AStoker/eInk-Projects/stand-4.2in/tools/mkdrawings.py

#!/usr/bin/env python3
"""Generate dimensioned drawing sheets from the OpenSCAD model's own parameters.

Reads /tmp/params.txt (produced by `openscad -D 'part="params"'`) so the drawings
can never drift from the STLs.  Emits one SVG fragment per sheet.
"""
import math, os, json, re

P = {}
for line in open(os.environ.get("PARAMS", "/tmp/params.txt")):
    line = line.strip()
    if not line or "=" not in line:
        continue
    k, v = line.split("=", 1)
    try:
        P[k] = float(v)
    except ValueError:
        P[k] = v

# ----------------------------------------------------------------- svg utils
AR = 1.6           # arrowhead length
TS = 3.0           # default text size
out = []


def esc(s):
    return (str(s).replace("&", "&amp;").replace("<", "&lt;").replace(">", "&gt;")
            .replace("\u00b7", "&#183;").replace("\u2264", "&#8804;")
            .replace("\u00b0", "&#176;").replace("\u00d7", "&#215;"))


def n(v):
    """format a number the way a drawing would"""
    if abs(v - round(v)) < 0.005:
        return f"{v:.0f}"
    return f"{v:.2f}".rstrip("0").rstrip(".")


class SVG:
    def __init__(self, w, h):
        self.w, self.h, self.b = w, h, []

    def add(self, s):
        self.b.append(s)

    def line(self, x1, y1, x2, y2, cls="edge"):
        self.add(f'<line class="{cls}" x1="{x1:.2f}" y1="{y1:.2f}" x2="{x2:.2f}" y2="{y2:.2f}"/>')

    def rect(self, x, y, w, h, cls="edge", r=0):
        self.add(f'<rect class="{cls}" x="{x:.2f}" y="{y:.2f}" width="{w:.2f}" '
                 f'height="{h:.2f}" rx="{r:.2f}"/>')

    def circ(self, x, y, d, cls="edge"):
        self.add(f'<circle class="{cls}" cx="{x:.2f}" cy="{y:.2f}" r="{d/2:.2f}"/>')

    def path(self, d, cls="edge"):
        self.add(f'<path class="{cls}" d="{d}"/>')

    def txt(self, x, y, s, cls="lbl", anchor="middle", size=TS, rot=None):
        tr = f' transform="rotate({rot} {x:.2f} {y:.2f})"' if rot else ""
        self.add(f'<text class="{cls}" x="{x:.2f}" y="{y:.2f}" text-anchor="{anchor}" '
                 f'font-size="{size}"{tr}>{esc(s)}</text>')

    # --- dimensioning -----------------------------------------------------
    def _ah(self, x, y, dx, dy):
        """arrowhead at (x,y) pointing along (dx,dy)"""
        m = math.hypot(dx, dy) or 1
        dx, dy = dx / m, dy / m
        px, py = -dy, dx
        return (f'M{x:.2f},{y:.2f} L{x-dx*AR+px*AR*0.32:.2f},{y-dy*AR+py*AR*0.32:.2f} '
                f'L{x-dx*AR-px*AR*0.32:.2f},{y-dy*AR-py*AR*0.32:.2f} Z')

    def dimh(self, x1, x2, y, label=None, ext_from=None, flip=False):
        if label is None:
            label = n(abs(x2 - x1))
        if ext_from is not None:
            for x in (x1, x2):
                self.line(x, ext_from, x, y + (1.2 if y > ext_from else -1.2), "ext")
        self.line(x1, y, x2, y, "dim")
        inside = abs(x2 - x1) > 9
        if inside:
            self.path(self._ah(x1, y, x1 - x2, 0), "arrow")
            self.path(self._ah(x2, y, x2 - x1, 0), "arrow")
        else:
            self.line(x1 - 4, y, x1, y, "dim")
            self.line(x2, y, x2 + 4, y, "dim")
            self.path(self._ah(x1, y, 1, 0), "arrow")
            self.path(self._ah(x2, y, -1, 0), "arrow")
        tx = (x1 + x2) / 2
        if inside:
            self.txt(tx, y - 1.3, label, "dimtxt")
        else:
            self.txt(tx, y - 1.6 if not flip else y + 3.4, label, "dimtxt")

    def dimv(self, y1, y2, x, label=None, ext_from=None):
        if label is None:
            label = n(abs(y2 - y1))
        if ext_from is not None:
            for y in (y1, y2):
                self.line(ext_from, y, x + (1.2 if x > ext_from else -1.2), y, "ext")
        self.line(x, y1, x, y2, "dim")
        inside = abs(y2 - y1) > 9
        if inside:
            self.path(self._ah(x, y1, 0, y1 - y2), "arrow")
            self.path(self._ah(x, y2, 0, y2 - y1), "arrow")
        else:
            self.line(x, y1 - 4, x, y1, "dim")
            self.line(x, y2, x, y2 + 4, "dim")
            self.path(self._ah(x, y1, 0, 1), "arrow")
            self.path(self._ah(x, y2, 0, -1), "arrow")
        self.txt(x - 1.3, (y1 + y2) / 2, label, "dimtxt", rot=-90)

    def leader(self, x, y, tx, ty, label, anchor="start"):
        self.line(x, y, tx, ty, "dim")
        self.path(self._ah(x, y, x - tx, y - ty), "arrow")
        off = 1.2 if anchor == "start" else -1.2
        self.txt(tx + off, ty + 1.0, label, "note", anchor)

    def note(self, x, y, label, anchor="start", size=2.7):
        self.txt(x, y, label, "note", anchor, size)

    def hatch(self, x, y, w, h, step=1.6):
        self.add(f'<g class="hatch" clip-path="url(#c{abs(hash((x,y,w,h)))%99999})">')
        self.add(f'<clipPath id="c{abs(hash((x,y,w,h)))%99999}">'
                 f'<rect x="{x:.2f}" y="{y:.2f}" width="{w:.2f}" height="{h:.2f}"/></clipPath>')
        k = -h
        while k < w:
            self.line(x + k, y + h, x + k + h, y, "hl")
            k += step
        self.add('</g>')

    def titleblock(self, x, y, w, h, name, sheet, of, scale, rev="E"):
        # the sheets are always drawn in the as-designed hand; this says whether
        # the exported STLs come out that way or mirrored
        self.txt(x, y - 2.4,
                 "STLs export flat-face-down and MIRRORED IN X (print_mirror = true)"
                 if MIRRORED else
                 "STLs export flat-face-down, as drawn (print_mirror = false)",
                 "note", "start", 2.35)
        self.rect(x, y, w, h, "tbframe")
        self.line(x, y + h * 0.5, x + w, y + h * 0.5, "tbrule")
        self.line(x + w * 0.55, y + h * 0.5, x + w * 0.55, y + h, "tbrule")
        self.line(x + w * 0.78, y + h * 0.5, x + w * 0.78, y + h, "tbrule")
        self.txt(x + 2, y + h * 0.34, name, "tbname", "start", 3.6)
        self.txt(x + 2, y + h * 0.85, f"UNITS mm · SCALE {scale}", "tbmeta", "start", 2.4)
        self.txt(x + w * 0.575, y + h * 0.85, f"SHEET {sheet}/{of}", "tbmeta", "start", 2.4)
        self.txt(x + w * 0.80, y + h * 0.85, f"REV {rev}", "tbmeta", "start", 2.4)


    def bal(self, x, y, num, tx, ty):
        self.line(x, y, tx, ty, "dim")
        self.path(self._ah(x, y, x - tx, y - ty), "arrow")
        self.circ(tx, ty, 5.6, "balloon")
        self.txt(tx, ty + 1.15, str(num), "baltxt", size=3.1)

    def notes(self, x, y, items, cw=46, title="NOTES"):
        import textwrap
        if title:
            self.txt(x, y, title, "vlabel", "start", 3.2)
            y += 6.5
        for num, text in items:
            self.circ(x + 2.8, y - 1.0, 5.6, "balloon")
            self.txt(x + 2.8, y + 0.15, str(num), "baltxt", size=3.1)
            lines = textwrap.wrap(text, cw) or [""]
            for j, ln in enumerate(lines):
                self.txt(x + 9, y + j * 3.7, ln, "note", "start", 2.7)
            y += max(1, len(lines)) * 3.7 + 2.8
        return y

    def render(self, ident):
        return (f'<svg class="dwg" id="{ident}" viewBox="0 0 {self.w} {self.h}" '
                f'xmlns="http://www.w3.org/2000/svg" role="img">'
                + "".join(self.b) + "</svg>")


# ------------------------------------------------------- standalone sheet CSS
# The sheets are written twice: as fragments in _sheets.json (styled by the page
# in tools/mkpage.py) and as standalone .svg files.  A standalone file has no
# page around it, so it carries its own copy of the drawing classes - that is
# what lets the README embed a sheet directly, and what makes a sheet readable
# when the file is opened on its own.
#
# The colours are written out literally, once per theme, rather than as CSS
# custom properties: an SVG loaded through <img> (which is how a README embeds
# one) is rendered by whatever engine the viewer has, and var() is the first
# thing a lightweight renderer drops - it takes the whole drawing to black.
LIGHT = dict(paper="#F1F3F0", surface="#FAFBF9", ink="#171B18", ink2="#59635C",
             rule="#D3D8D2", accent="#0E6B57", verify="#A8631A", partf="#E4E8E3",
             glass="#D9E4E6", pcbf="#CBDCCF", cellf="#D2D6D8", chgf="#C7D8E4",
             platf="#EDEFEA", bossf="#DCE2DA", padf="#D8DED6", voidf="#E7EAE5")
DARK  = dict(paper="#0F1211", surface="#171B18", ink="#E8ECE7", ink2="#93A099",
             rule="#2C332E", accent="#57CFA9", verify="#E0A64B", partf="#232A26",
             glass="#243233", pcbf="#1F3327", cellf="#2A3033", chgf="#1E2E3A",
             platf="#1C221E", bossf="#28302B", padf="#2A322C", voidf="#101413")

RULES = """
svg{{font-family:"IBM Plex Mono",ui-monospace,monospace}}
.bg{{fill:{paper};stroke:none}}
.part{{fill:{partf};stroke:{ink};stroke-width:.55}}
.edge{{fill:none;stroke:{ink};stroke-width:.5}}
.inkline{{fill:none;stroke:{ink};stroke-width:1.1}}
.ghost{{fill:none;stroke:{rule};stroke-width:.45}}
.hid{{fill:none;stroke:{ink2};stroke-width:.35;stroke-dasharray:2.2 1.4}}
.cl{{fill:none;stroke:{ink2};stroke-width:.28;stroke-dasharray:6 1.6 1 1.6;opacity:.75}}
.cut{{fill:{paper};stroke:{ink};stroke-width:.45}}
.ink{{fill:{ink};opacity:.86;stroke:none}}
.glass{{fill:{glass};stroke:{ink};stroke-width:.4}}
.pcb{{fill:{pcbf};stroke:{ink};stroke-width:.45}}
.cell{{fill:{cellf};stroke:{ink};stroke-width:.45}}
.chg{{fill:{chgf};stroke:{ink};stroke-width:.4}}
.plat{{fill:{platf};stroke:{ink2};stroke-width:.35}}
.boss{{fill:{bossf};stroke:{ink2};stroke-width:.35}}
.pad{{fill:{padf};stroke:{ink2};stroke-width:.35}}
.voidfill{{fill:{voidf};stroke:{ink2};stroke-width:.35}}
.warn{{fill:none;stroke:{verify};stroke-width:.6;stroke-dasharray:2 1.2}}
.wire{{fill:none;stroke:{ink};stroke-width:.62;stroke-linejoin:round}}
.wire.ntc{{stroke:{verify}}}
.clash{{fill:{verify};fill-opacity:.30;stroke:{verify};stroke-width:.7}}
.clashtxt{{fill:{verify};font-weight:600;letter-spacing:.02em}}
.res{{fill:{surface};stroke:{ink};stroke-width:.5}}
.leg{{stroke:{ink};stroke-width:2.6;stroke-linecap:round;fill:none}}
.table{{stroke:{ink2};stroke-width:.6}}
.com{{fill:{verify};stroke:{ink};stroke-width:.3}}
.hl{{stroke:{rule};stroke-width:.3;fill:none}}
.hatch{{opacity:.9}}
.dim{{fill:none;stroke:{accent};stroke-width:.32}}
.ext{{fill:none;stroke:{accent};stroke-width:.22;opacity:.55}}
.arrow{{fill:{accent};stroke:none}}
.dimtxt{{fill:{accent};letter-spacing:.02em}}
.note{{fill:{ink2}}}
.val{{fill:{ink};font-weight:600}}
.val.warn{{fill:{verify};stroke:none}}
.balloon{{fill:{surface};stroke:{accent};stroke-width:.45}}
.baltxt{{fill:{accent};font-weight:600;text-anchor:middle}}
.vlabel{{fill:{ink};font-weight:600;letter-spacing:.09em}}
.cmp{{fill:{ink};font-weight:600}}
.cmpsub{{fill:{ink2}}}
.tbframe{{fill:none;stroke:{ink};stroke-width:.5}}
.tbrule{{stroke:{rule};stroke-width:.35;fill:none}}
.tbname{{fill:{ink};font-weight:700;letter-spacing:.03em}}
.tbmeta{{fill:{ink2};letter-spacing:.09em}}
"""

SVG_CSS = (RULES.format(**LIGHT)
           + "@media (prefers-color-scheme:dark){" + RULES.format(**DARK) + "}")


def standalone(sv):
    """Wrap a sheet fragment as a file that renders on its own.

    Size and background come from the fragment's own viewBox - sheet 8 is a
    taller sheet than the rest, and a hard-coded background left it striped.
    """
    w, h = (float(v) for v in re.search(r'viewBox="0 0 ([\d.]+) ([\d.]+)"', sv).groups())
    return ('<?xml version="1.0" encoding="UTF-8"?>\n'
            + sv.replace('class="dwg"', f'class="dwg" width="{w*4:.0f}" height="{h*4:.0f}"')
                .replace('role="img">',
                         f'role="img"><style>{SVG_CSS}</style>'
                         f'<rect class="bg" x="0" y="0" width="{w:.0f}" height="{h:.0f}"/>', 1))


# ------------------------------------------------------------------ geometry
W, H, D = P["W"], P["H"], P["depth"]
FLASH = bool(P.get("flash_port", 0))          # is the driver board's USB-C cut through?
MIRRORED = bool(P.get("print_mirror", 0))     # do the STLs come out the opposite hand?
HEADER = bool(P.get("mod_header", 0))         # is a mated module header being allowed for?
BARE   = bool(P.get("bare_panel", 0))         # panel with no PCB behind it?
INSERT = bool(P.get("insert_fit", 0))         # heat-set inserts, or self-tapping?
PERF   = bool(P.get("perf_fit", 0))           # is a separate divider board fitted?
CARRIER= bool(P.get("carrier_fit", 0))        # driver on a carrier perfboard?
MAGS   = bool(P.get("mag_fit", 0))            # fridge magnets in the back face?
SNAP   = bool(P.get("port_snap", 0))          # rear port is a snap-in pigtail?
CLAMP  = bool(P.get("pivot_screw", 0))        # hinge is a clamp screw, not a pin?
FAST   = (f"M3 heat-set inserts (bore dia {P['ins_d']:g} x {P['ins_l']+1:g} deep) with countersunk screws"
          if INSERT else "self-tapping screws")
# screw positions, [x, z].  Bare panel: one near each corner, through the end
# walls.  Module: the old single spine of three, all on the +X side.
SCR = ([(-P["scr_cx"], P["scr_cz"]), (P["scr_cx"], P["scr_cz"]),
        (-P["scr_cx"], P["H"]-P["scr_cz"]), (P["scr_cx"], P["H"]-P["scr_cz"])] if BARE
       else [(P["scr_x"], P["scr_z0"]), (P["scr_x"], P["scr_z1"]), (P["scr_x"], P["scr_z2"])])
P["flash_skin"] = P["flash_wall"]             # material left outboard of a closed jack
cav_x0, cav_x1 = P["cav_x0"], P["cav_x1"]
cav_z0, cav_z1 = P["cav_z0"], P["cav_z1"]
cav_w, cav_h = P["cav_w"], P["cav_h"]
Zc = P["Zc"]
# ---- the stand, PORTRAIT ONLY.  The leg pivots directly in a recess in the
# cover, so every stand view on these sheets is a rectangle and an arc.
piv_z, piv_y, piv_h = P["piv_z"], P["piv_y"], P["piv_h"]
rec_w, rec_top, rec_y0 = P["rec_w"], P["rec_top"], P["rec_y0"]
rec_z0 = P["rec_z0"]                           # recess, bottom end (derived in the model)
DEP    = P["dep_ang"]
win_w, win_h = P["win_w"], P["win_h"]
SW, SH = 268, 190
TBX, TBY = SW - 96 - 6, SH - 18 - 5

def mk(w=SW, h=SH):
    return SVG(w, h)

# The port opening, as the model actually cuts it.  With port_snap the pigtail's
# own catch holds it: the opening is snap_w x snap_h plus clearance and there is
# nothing printed around it.  Without it, a breakout board sits in printed rails
# behind a smaller port_w x port_h receptacle hole.  Drawing the rails
# unconditionally showed features this build does not have.
def port_opening(s, mx, mz, cls="cut"):
    if SNAP:
        w = P["snap_w"] + 2*P["snap_c"]
        h = P["snap_h"] + 2*P["snap_c"]
        s.rect(mx(P["ucb_x"] - w/2), mz(P["ucb_z"] + h/2), w, h, cls, 0.6)
        return w, h
    for sz in (-1, 1):
        s.rect(mx(P["ucb_x"] - (P["ucb_w"]+4)/2),
               mz(P["ucb_z"] + sz*(P["ucb_t"]/2+0.15+1.0) + 1.0),
               P["ucb_w"]+4, 2.0, "boss")
    s.rect(mx(P["ucb_x"] - P["port_w"]/2), mz(P["ucb_z"] + P["port_h"]/2),
           P["port_w"], P["port_h"], cls, 1.2)
    return P["port_w"], P["port_h"]


def views(s, ox, oy):
    return (lambda x: ox + x + W/2), (lambda z: oy + (H - z))

# ============================================================ SHEET 1
def sheet1():
    s = mk()
    oy = 15
    fx, fz = views(s, 24, oy)

    s.rect(fx(-W/2), fz(H), W, H, "part", P["corner_r"])
    s.rect(fx(-win_w/2), fz(Zc + win_h/2), win_w, win_h, "edge", 3)
    s.rect(fx(-P["act_w"]/2), fz(Zc + P["act_h"]/2), P["act_w"], P["act_h"], "ink")
    s.rect(fx(P["pcb_px"]-P["pcb_w"]/2), fz(Zc+P["pcb_h"]/2), P["pcb_w"], P["pcb_h"], "hid")
    s.line(fx(0), fz(H)-4, fx(0), fz(0)+4, "cl")
    s.line(fx(-W/2)-4, fz(Zc), fx(W/2)+4, fz(Zc), "cl")
    s.txt(fx(0), fz(H)-8, "FRONT", "vlabel")
    s.dimh(fx(-W/2), fx(W/2), fz(0)+16, n(W), ext_from=fz(0))
    s.dimv(fz(H), fz(0), fx(-W/2)-13, n(H), ext_from=fx(-W/2))
    s.dimh(fx(-win_w/2), fx(win_w/2), fz(0)+8, n(win_w), ext_from=fz(Zc-win_h/2))
    s.dimv(fz(Zc+win_h/2), fz(Zc-win_h/2), fx(-W/2)-5, n(win_h), ext_from=fx(-win_w/2))
    s.dimh(fx(-W/2), fx(-win_w/2), fz(H)-5, n(W/2-win_w/2), ext_from=fz(Zc+win_h/2))
    s.dimh(fx(win_w/2), fx(W/2), fz(H)-5, n(W/2-win_w/2), ext_from=fz(Zc+win_h/2))
    s.dimv(fz(H), fz(Zc+win_h/2), fx(W/2)+6, n(H/2-win_h/2), ext_from=fx(win_w/2))
    s.dimv(fz(Zc-win_h/2), fz(0), fx(W/2)+6, n(H/2-win_h/2), ext_from=fx(win_w/2))
    s.bal(fx(-win_w/2+0.7), fz(Zc+win_h/2-4), 1, fx(-win_w/2-6), fz(Zc+win_h/2+7))
    s.bal(fx(-W/2+2.4), fz(2.4), 2, fx(-W/2+11), fz(11))

    # side
    sx = 124
    yx = lambda y: sx + y
    s.rect(yx(0), fz(H), D, H, "part")
    s.line(yx(P["body_d"]), fz(H), yx(P["body_d"]), fz(0), "hid")
    ch, rc = P["front_chf"], P["rear_chf"]
    s.line(yx(0), fz(H)+ch, yx(ch), fz(H), "edge")
    s.line(yx(0), fz(0)-ch, yx(ch), fz(0), "edge")
    s.line(yx(D-rc), fz(H), yx(D), fz(H)+rc, "edge")
    s.line(yx(D-rc), fz(0), yx(D), fz(0)-rc, "edge")
    # the flash opening only exists if the model cuts it; otherwise the wall is
    # solid and all that is behind it is a blind pocket, drawn hidden
    s.rect(yx(P["flash_y0"]), fz(H), P["flash_y1"]-P["flash_y0"], 1.6,
           "cut" if FLASH else "hid")
    s.rect(yx(D-1.0), fz(P["ucb_z"]+P["port_h"]/2), 1.0, P["port_h"], "cut")
    s.txt(yx(D/2), fz(H)-8, "RIGHT", "vlabel")
    s.dimh(yx(0), yx(D), fz(0)+16, n(D), ext_from=fz(0))
    s.bal(yx(D-rc/2), fz(H)+rc/2, 3, yx(D)+9, fz(H)-6)
    s.bal(yx(ch/2), fz(0)-ch/2, 4, yx(D)+9, fz(0)+8)
    s.bal(yx((P["flash_y0"]+P["flash_y1"])/2), fz(H)+0.8, 5, yx(D)+9, fz(H)+9)
    s.bal(yx(D), fz(P["ucb_z"]), 6, yx(D)+9, fz(P["ucb_z"])+2)
    s.bal(yx(P["body_d"]), fz(30), 7, yx(D)+9, fz(30))

    # back
    bx = 156
    gx = lambda x: bx + x + W/2
    s.rect(gx(-W/2), fz(H), W, H, "part", P["corner_r"])
    s.rect(gx(-rec_w/2), fz(rec_top), rec_w, rec_top-rec_z0, "edge", 1)
    s.rect(gx(-P["leg_w"]/2), fz(piv_z+P["heel_z"]), P["leg_w"],
           piv_z+P["heel_z"]-P["foot_z"], "hid", 1)
    pw, ph = port_opening(s, gx, fz)
    for (sx, sz) in SCR:
        s.circ(gx(sx), fz(sz), P["scr_head"], "cut")
    s.line(gx(0), fz(H)-4, gx(0), fz(0)+4, "cl")
    s.line(gx(-W/2)-4, fz(piv_z), gx(W/2)+4, fz(piv_z), "cl")
    s.txt(gx(0), fz(H)-8, "BACK", "vlabel")
    s.dimv(fz(piv_z), fz(0), gx(-W/2)-8, n(piv_z), ext_from=gx(-W/2))
    s.dimh(gx(0), gx(P["ucb_x"]), fz(0)+8, n(abs(P["ucb_x"])), ext_from=fz(P["ucb_z"]))
    s.dimv(fz(P["ucb_z"]), fz(0), gx(P["ucb_x"])-8, n(P["ucb_z"]), ext_from=gx(P["ucb_x"]))
    s.dimh(gx(SCR[-1][0]), gx(W/2), fz(H)-5, n(W/2-SCR[-1][0]), ext_from=fz(SCR[-1][1]))
    s.bal(gx(P["ucb_x"]+pw/2), fz(P["ucb_z"]), 6, gx(P["ucb_x"]+18), fz(P["ucb_z"])+9)
    s.bal(gx(SCR[0][0]), fz(SCR[0][1]), 8, gx(SCR[0][0])-11, fz(SCR[0][1])+8)
    s.bal(gx(rec_w/2), fz(piv_z+8), 9, gx(rec_w/2)+10, fz(piv_z+8)-7)

    y = s.notes(22, 143, [
        (1, f"panel white border {n(P['white_show_short'])} visible on the short axis, "
            f"{n(P['white_show_long'])} on the long axis"),
        (2, f"outer corners R{n(P['corner_r'])}"),
        (3, f"{n(rc)} x 45 deg chamfer on all four back edges. It moves the contact edge forward - see sheet 7"),
        (4, f"{n(ch)} x 45 deg chamfer on the front face"),
    ], cw=44)
    s.notes(108, 143, [
        (5, f"USB-C flash port, {n(P['usb_w'])} wide, top wall (driver board)"
            if FLASH else
            f"driver-board USB-C, {n(P['usb_w'])} wide - blind pocket, the top wall "
            f"is solid ({n(P['wall'])} thick, {n(P['flash_skin'])} of skin left). "
            f"The charge port is the only opening"),
        (6, f"USB-C charge port {n(P['port_w'])} x {n(P['port_h'])}, back face"),
        (7, "frame / cover seam"),
    ], cw=44, title=" ")
    s.notes(190, 143, [
        (8, f"4 x cover screws, one near each corner: {n(P['scr_cx'])} from the centreline, {n(P['scr_cz'])} from each end. {FAST}"
            if BARE else
            f"3 x M2.5 cover screws, {n(P['scr_x'])} from the centreline"),
        (9, f"kickstand leg {n(P['leg_w'])} wide, folded FLUSH in a {n(rec_w)} recess; "
            f"pivot {n(piv_z)} up. The folded foot stops at z {n(P['foot_z'])}, clear of the "
            f"{n(rc)} chamfer, so nothing overhangs the bottom edge"),
    ], cw=40, title=" ")
    s.titleblock(TBX, TBY, 96, 18, "ASSEMBLY / ENVELOPE", 1, 8, "1:1")
    return s.render("s1")


# ============================================================ SHEET 2
def sheet2():
    s = mk()
    ox, oy = 28, 14
    fx, fz = views(s, ox, oy)
    s.rect(fx(-W/2), fz(H), W, H, "ghost", P["corner_r"])
    s.rect(fx(cav_x0), fz(cav_z1), cav_w, cav_h, "part", P["cav_r"])
    s.rect(fx(-rec_w/2), fz(rec_top), rec_w, rec_top-rec_z0, "hid", 1)
    # fridge magnet pockets - blind in the BACK face, so hidden from in here
    if MAGS:
        for mx, mz in ((P["mag_x"], P["mag_z0"]), (-P["mag_x"], P["mag_z1"])):
            s.circ(fx(mx), fz(mz), P["mag_bd"], "boss")   # the boss, on this face
            s.circ(fx(mx), fz(mz), P["mag_bore"], "hid")  # the pocket, behind it
    # the register extension: the plate that floors the shallow end of the pocket.
    # It stops short of the bottom edge on purpose - see note 1.
    s.rect(fx(-P["stand_reg_w"]/2), fz(P["shl_z0"]+0.05),
           P["stand_reg_w"], (P["shl_z0"]+0.05)-P["reg_ext_z0"], "boss")

    # ---- the cell, bottom band, centred
    bx0, bz0 = P["bat_x0"], P["bat_cz"]-P["bat_h"]/2
    s.rect(fx(bx0), fz(bz0+P["bat_h"]), P["bat_w"], P["bat_h"], "cell", 2)
    s.txt(fx(P["bat_cx"]), fz(P["bat_cz"])-1.4, "LiPo 2000 mAh  ·  694449", "cmp", size=3.0)
    s.txt(fx(P["bat_cx"]), fz(P["bat_cz"])+2.6,
          f"{n(P['bat_w'])} x {n(P['bat_h'])} x {n(P['bat_t'])}", "cmpsub", size=2.6)
    s.txt(fx(P["bat_cx"]), fz(P["bat_cz"])+6.2, "red +  ·  black -  ·  yellow NTC", "cmpsub", size=2.25)
    for sx in (-1, 1):   # X fences
        s.rect(fx(P["bat_cx"]+sx*(P["bat_w"]/2+P["bat_clr"]) - (0 if sx>0 else P["bat_fence"])),
               fz(bz0+P["bat_h"]), P["bat_fence"], P["bat_h"], "boss")

    # ---- the charger.  On a Perma-Proto when there is one, on its own
    #      standoffs when there is not.
    px0, pz0 = P["proto_x0"], P["proto_z0"]
    if not BARE:
        s.rect(fx(px0), fz(P["proto_z1"]), P["proto_w"], P["proto_h"], "pcb", 1.5)
        s.txt(fx(P["proto_cx"]), fz(P["proto_z1"]-13.5), "PERMA-PROTO", "cmp", size=3.0)
        s.txt(fx(P["proto_cx"]), fz(P["proto_z1"]-17.5),
              f"quarter {n(P['proto_w'])} x {n(P['proto_h'])}", "cmpsub", size=2.6)
        for sz in (-1, 1):
            s.circ(fx(P["proto_cx"]), fz(P["proto_cz"]+sz*P["proto_hole_sp"]/2), 3.2, "cut")
    cgx = P["chg_x_c"] if BARE else P["chg_x"]
    s.rect(fx(cgx-P["chg_w"]/2), fz(P["chg_z"]+P["chg_h"]/2), P["chg_w"], P["chg_h"], "chg", 1)
    s.txt(fx(cgx), fz(P["chg_z"])-0.6, P["chg_part"], "cmp", size=2.8)
    s.txt(fx(cgx), fz(P["chg_z"])+3.0, f"{n(P['chg_w'])} x {n(P['chg_h'])}", "cmpsub", size=2.5)
    if BARE:
        for sx in (-1, 1):
            for sz in (-1, 1):
                cx_, cz_ = fx(cgx+sx*P["chg_hx"]/2), fz(P["chg_z"]+sz*P["chg_hz"]/2)
                s.circ(cx_, cz_, P["chg_boss_d"], "boss")
                s.circ(cx_, cz_, P["chg_ins_d"], "cut")

    if CARRIER:
        s.rect(fx(P["carrier_cx"]-P["carrier_w"]/2), fz(P["carrier_cz"]+P["carrier_h"]/2),
               P["carrier_w"], P["carrier_h"], "plat", 1.0)
        s.txt(fx(P["carrier_cx"]), fz(P["carrier_z0"]+9.0),
              f"CARRIER {n(P['carrier_w'])} x {n(P['carrier_h'])}", "cmp", size=2.6)
        s.txt(fx(P["carrier_cx"]), fz(P["carrier_z0"]+5.2),
              "divider on the spare", "cmpsub", size=2.3)
        for sx_ in (-1, 1):
            for sz in (-1, 1):
                cx_ = fx(P["carrier_cx"]+sx_*P["carrier_hx"]/2)
                cz_ = fz(P["carrier_cz"]+sz*P["carrier_hz"]/2)
                s.circ(cx_, cz_, P["carrier_pad"], "boss")
                s.circ(cx_, cz_, P["carrier_hole"]-P["carrier_peg"], "cut")
    s.rect(fx(P["drv_x0"]), fz(P["drv_z1"]), P["drv_w"], P["drv_h"], "pcb", 1.5)
    s.txt(fx(P["drv_cx"]), fz(P["drv_cz"])-3.4, "WAVESHARE", "cmp", size=2.9)
    s.txt(fx(P["drv_cx"]), fz(P["drv_cz"])+0.2, "ESP32 DRIVER", "cmp", size=2.9)
    s.txt(fx(P["drv_cx"]), fz(P["drv_cz"])+3.8, f"{n(P['drv_w'])} x {n(P['drv_h'])}", "cmpsub", size=2.6)
    s.rect(fx(P["flash_x"]-4.5), fz(P["drv_z1"]+2.6), 9, 1.4,
           "cut" if FLASH else "hid")   # driver USB-C at the top wall
    for sx in (-1, 1):   # driver rails
        rc = P["drv_cx"] + sx*(P["drv_w"]/2 + P["drv_clr"] + P["drv_rail"]/2 - 1.0)
        s.rect(fx(rc-P["drv_rail"]/2), fz(P["drv_cz"]+(P["drv_h"]-1)/2),
               P["drv_rail"], P["drv_h"]-1, "boss")
    if BARE:
        # the 24-pin socket on the board's -X edge, and the slot the ribbon
        # arrives through.  The two line up: that is what the board's position
        # along Z is for.
        s.rect(fx(P["drv_x0"]-1.2), fz(P["fpc_z"]+P["fpc_w"]/2), 2.4, P["fpc_w"], "com", 0.4)
        s.txt(fx(P["drv_x0"])-14, fz(P["fpc_z"])-3.0, "24-pin FPC", "cmp", size=2.5)
        s.txt(fx(P["drv_x0"])-14, fz(P["fpc_z"])+0.6, "the panel plugs", "cmpsub", size=2.3)
        s.txt(fx(P["drv_x0"])-14, fz(P["fpc_z"])+3.8, "straight in here", "cmpsub", size=2.3)
        rz0 = P["rib_cz"] - P["rib_w"]/2
        s.rect(fx(-W/2+P["wall_rib"]), fz(rz0+P["rib_w"]), P["rib_clr"], P["rib_w"], "warn")
        s.dimv(fz(P["fpc_z"]+P["fpc_w"]/2), fz(P["fpc_z"]-P["fpc_w"]/2), fx(P["drv_x0"])-30,
               n(P["fpc_w"]), ext_from=fx(P["drv_x0"]))

    # ---- module retention pads: only when there is a module PCB to hold
    if not BARE:
        for (px, pz) in ((P["pad_x0"], P["pad_z0"]), (P["pad_x1"], P["pad_z1"])):
            s.rect(fx(px-P["pad_w"]/2), fz(pz+P["pad_h"]/2), P["pad_w"], P["pad_h"], "pad", 0.8)
    else:
        for (sx, sz) in SCR:            # the four corner posts and their screws
            s.rect(fx(sx-P["post_s"]/2), fz(sz+P["post_s"]/2),
                   P["post_s"], P["post_s"], "boss", 1.0)
            s.circ(fx(sx), fz(sz), P["scr_head"], "cut")
    if SNAP:
        s.rect(fx(P["ucb_x"]-P["snap_w"]/2), fz(P["ucb_z"]+P["snap_h"]/2),
               P["snap_w"], P["snap_h"], "cut", 0.6)
    else:
        s.rect(fx(P["ucb_x"]-P["ucb_w"]/2), fz(P["ucb_z"]+2.6), P["ucb_w"], 5.2, "chg", 0.8)
    # module header keep-out - only when one is actually fitted.  On this build
    # the panel's 24-pin FPC goes straight into the driver board, so there is
    # nothing standing off the back of the module and nothing to draw.
    if HEADER:
        s.rect(fx(P["conn_x"]-P["conn_w"]/2), fz(P["conn_z"]+P["conn_l"]/2),
               P["conn_w"], P["conn_l"], "warn")
        s.hatch(fx(P["conn_x"]-P["conn_w"]/2), fz(P["conn_z"]+P["conn_l"]/2),
                P["conn_w"], P["conn_l"], step=2.0)

    # ---- dimensions ------------------------------------------------------
    y1, y2, y3 = 128, 136.5, 145
    s.dimh(fx(cav_x0), fx(bx0), y1, n(bx0-cav_x0), ext_from=fz(bz0))
    s.dimh(fx(bx0), fx(bx0+P["bat_w"]), y1, n(P["bat_w"]), ext_from=fz(bz0))
    s.dimh(fx(bx0+P["bat_w"]), fx(cav_x1), y1, n(cav_x1-bx0-P["bat_w"]), ext_from=fz(bz0))
    if BARE:
        s.dimh(fx(P["drv_x0"]), fx(P["drv_x1"]), y2, n(P["drv_w"]), ext_from=fz(P["drv_z0"]))
        s.dimh(fx(P["drv_x1"]), fx(P["bat_x0"]), y2, n(P["bat_x0"]-P["drv_x1"]), ext_from=fz(P["drv_z0"]))
        s.dimh(fx(P["chg_x_c"]-P["chg_w"]/2), fx(P["chg_x_c"]+P["chg_w"]/2), y2, n(P["chg_w"]),
               ext_from=fz(P["chg_z"]+P["chg_h"]/2))
    else:
        s.dimh(fx(px0), fx(P["proto_x1"]), y2, n(P["proto_w"]), ext_from=fz(pz0))
        s.dimh(fx(P["proto_x1"]), fx(P["drv_x0"]), y2, n(P["drv_x0"]-P["proto_x1"]), ext_from=fz(pz0))
        s.dimh(fx(P["drv_x0"]), fx(P["drv_x1"]), y2, n(P["drv_w"]), ext_from=fz(P["drv_z0"]))
    s.dimh(fx(cav_x0), fx(cav_x1), y3, n(cav_w), ext_from=fz(cav_z0))

    if BARE:
        s.dimv(fz(P["chg_z"]+P["chg_h"]/2), fz(P["chg_z"]-P["chg_h"]/2), 22, n(P["chg_h"]),
               ext_from=fx(P["chg_x_c"]-P["chg_w"]/2))
    else:
        s.dimv(fz(P["proto_z1"]), fz(pz0), 22, n(P["proto_h"]), ext_from=fx(px0))
    s.dimv(fz(P["ucb_z"]), fz(0), 22, n(P["ucb_z"]), ext_from=fx(P["ucb_x"]))
    s.dimv(fz(P["drv_z1"]), fz(P["drv_z0"]), 114, n(P["drv_h"]), ext_from=fx(P["drv_x1"]))
    s.dimv(fz(bz0+P["bat_h"]), fz(bz0), 114, n(P["bat_h"]), ext_from=fx(bx0+P["bat_w"]))
    s.dimv(fz(cav_z1), fz(cav_z0), 124, n(cav_h), ext_from=fx(cav_x1))

    # ---- balloons --------------------------------------------------------
    s.bal(fx(P["ucb_x"]), fz(P["ucb_z"]), 1, 9, fz(P["ucb_z"])+9)
    s.bal(fx(P["pad_x1"]), fz(P["pad_z1"]), 2, 133, 100)
    s.bal(fx(rec_w/2), fz(piv_z-14), 3, 132, 119)
    if BARE:
        s.bal(fx(SCR[2][0]), fz(SCR[2][1]), 4, 12, 30)
        s.bal(fx(P["chg_x_c"]-P["chg_w"]/2+2), fz(P["chg_z"]+P["chg_h"]/2-2), 5, 10, 46)
    else:
        s.bal(fx(P["proto_cx"]), fz(P["proto_cz"]+P["proto_hole_sp"]/2), 4, 12, fz(P["proto_cz"]+P["proto_hole_sp"]/2)+3)
        s.bal(fx(P["chg_x"]-P["chg_w"]/2+2), fz(P["chg_z"]+P["chg_h"]/2-2), 5, 10, 46)
    s.bal(fx(P["drv_x1"]-P["drv_rail"]/2), fz(P["drv_cz"]+16), 6, 132, 40)
    if HEADER:
        s.bal(fx(P["conn_x"]+P["conn_w"]/2), fz(P["conn_z"]), 7, 133, 113)
    s.txt(fx(0), 9, "LOOKING INTO THE OPEN BACK", "vlabel")

    clash = P["conn_h"] - (P["rec_back"] - P["bat_t"] - P["mod_back"])
    notes = [
        (1, f"USB-C pigtail, snapped into a {n(P['snap_w']+2*P['snap_c'])} x {n(P['snap_h']+2*P['snap_ch'])} opening in the back cover - its own catch holds it, so there is nothing printed around it. Two wires to the {P['chg_part']}"
            if SNAP else
            "USB-C charge breakout, on edge in printed rails, receptacle flush with the back cover. Two wires up the -X wall to the "
            f"{P['chg_part']}"),
        (2, f"glass retention ribs on the cover, {n(P['pad_w0'])} and {n(P['pad_w1'])} wide x {n(P['pad_h'])}: the interior is open behind the glass - it has to be, or the glass could not get in - so these press it against the front lip"
            if BARE else
            f"module retention pads {n(P['pad_w'])} x {n(P['pad_h'])}, one each side of the cell. Foam tape on the faces takes up the tolerance stack"),
        (3, f"stand recess, {n(rec_w)} wide x {n(rec_top-rec_z0)} long on the centreline. Floor at depth {n(rec_y0)}, leaving {n(P['rec_floor'])}, so it reaches depth {n(P['rec_back'])}. The driver carrier misses this band entirely (x {n(P['drv_x0'])} to {n(P['drv_x1'])} against +/-{n(rec_w/2)}); the cell crosses it and rides a platform level with it"),
        (4, f"4 x cover screws into {n(P['post_s'])} x {n(P['post_s'])} corner posts, which start at depth {n(P['post_y0'])} so the glass still passes them on its way into its pocket. {FAST}"
            if BARE else
            f"2 x M2.5 posts, {n(P['proto_hole_sp'])} apart, behind the Perma-Proto; the {P['chg_part']} rides on its front face"),
        (5, f"{P['chg_part']} charger breakout {n(P['chg_w'])} x {n(P['chg_h'])} x {n(P['chg_t'])}, on four standoff pads above the cell"
            if BARE else
            f"{P['chg_part']} charger breakout {n(P['chg_w'])} x {n(P['chg_h'])} x {n(P['chg_t'])}, low end of the Perma-Proto, nearest the charge port"),
        (6, f"driver board plugs into female headers on the carrier - the case holds the carrier, not the board. Stood on its long edge so the 24-pin FPC socket faces the ribbon slot, and slid along until the two line up"
            if CARRIER else
            f"driver board stood on its long edge so the 24-pin FPC socket faces the ribbon slot, and slid along until the two line up. Rails {n(P['drv_rail'])} wide, overlapping the PCB {n(P['drv_rail']-1)} each side"
            if BARE else
            f"driver-board rails {n(P['drv_rail'])} wide, overlapping the PCB {n(P['drv_rail']-1)} each side"),
    ]
    if HEADER:
        notes.append(
            (7, f"MODULE 8-PIN HEADER KEEP-OUT {n(P['conn_w'])} x {n(P['conn_l'])} x {n(P['conn_h'])} deep, position ASSUMED. Clashes with the cell by {n(clash)} - DO NOT PRINT, see below"))
    y = s.notes(150, 20, notes, cw=56)

    s.notes(150, y+2, [], title="MEASURE BEFORE YOU PRINT")
    ty = y + 8
    need = P["conn_h"] + P["bat_t"] + P["mod_back"] + 5.95 + 0.5
    if HEADER:
        s.txt(150, ty, "Three numbers on the module settle this sheet:", "note", "start", 2.65)
        items = [("a   header edge, and where across X", "conn_dz, conn_dx"),
                 ("b   header stand-off, mated, with the bend", f"conn_h  (assumed {n(P['conn_h'])})"),
                 ("c   is the glass centred on the PCB in Z?", "pan_off_z, act_off_z")]
        tail = [f"The board band clears a {n(P['conn_h'])} mm header ({n(P['proto_face']-P['mod_back'])} available);",
                f"the cell band does not ({n(P['rec_back']-P['bat_t']-P['mod_back'])}). If the header is on",
                "the cell's edge the two bands swap, which also",
                "moves the flash port to the opposite wall. Or",
                f"keep this layout and set depth = {n(need)}."]
    else:
        s.txt(150, ty, "Three numbers still settle this sheet:", "note", "start", 2.65)
        items = [("a   driver stack: board, parts and headers", f"drv_env {n(P['drv_env'])} + hdr_h {n(P['hdr_h'])}"),
                 ("b   panel ribbon, glass edge to the plug", "sets where the driver can sit"),
                 ("c   the rear pigtail's actual body size", f"snap_w / snap_h ({n(P['snap_w'])} x {n(P['snap_h'])})")]
        tail = ["The panel's 24-pin FPC plugs straight into the",
                "driver - no adapter if the board sits where the",
                f"ribbon reaches. The {n(P['fpc_w'])} socket is on one long",
                f"edge, {n(P['fpc_off'])} from the near end.",
                f"Driver face to glass: {n(P['drv_back']-P['drv_t']-P['mod_back'])} for parts {n(P['drv_env']-P['drv_t'])} proud."]
    for i, (lab, par) in enumerate(items):
        yy = ty + 6.5 + i*7.4
        s.txt(150, yy, lab, "note", "start", 2.65)
        s.txt(157, yy + 3.7, par, "val", "start", 2.65)
    for i, t in enumerate(tail):
        s.txt(150, ty + 30 + i*3.8, t, "note", "start", 2.65)
    s.titleblock(TBX, TBY, 96, 18, "INTERNAL LAYOUT", 2, 8, "1:1")
    return s.render("s2")


# ============================================================ SHEET 3
def sheet3():
    s = mk()
    SC = 5.2
    ox, oy = 24, 30
    ys = lambda y: ox + y*SC
    zs = lambda z: oy + (100 - z)*1.02
    top, bot = zs(100), zs(0)

    s.rect(ys(0), top, P["front_t"]*SC, bot-top, "part"); s.hatch(ys(0), top, P["front_t"]*SC, bot-top)
    s.rect(ys(P["cov_in"]), top, P["cover_t"]*SC, bot-top, "part"); s.hatch(ys(P["cov_in"]), top, P["cover_t"]*SC, bot-top)
    zr0, zr1 = zs(min(rec_top, 100)), zs(max(rec_z0, 0))
    s.rect(ys(P["rec_back"]), zr0, (D-P["rec_back"])*SC, zr1-zr0, "part")
    s.hatch(ys(P["rec_back"]), zr0, (rec_y0-P["rec_back"])*SC, zr1-zr0)
    s.rect(ys(rec_y0), zr0+3, P["rec_dep"]*SC, zr1-zr0-6, "voidfill")
    s.txt(ys(rec_y0+P["rec_dep"]/2), zs(40), "stand", "note", size=2.5)
    s.txt(ys(rec_y0+P["rec_dep"]/2), zs(36.5), "recess", "note", size=2.5)

    s.rect(ys(P["front_t"]), zs(96), P["pan_t"]*SC, zs(14)-zs(96), "glass")
    s.rect(ys(P["pcb_face_y"]), zs(98), P["pcb_t"]*SC, zs(12)-zs(98), "pcb")
    clr = P["rec_back"] - P["bat_t"] - P["mod_back"]
    if HEADER:
        s.rect(ys(P["mod_back"]), zs(62), P["conn_h"]*SC, zs(44)-zs(62), "warn")
        s.txt(ys(P["mod_back"]+clr/2), zs(51.5), "8-pin", "cmp", size=2.6)
        s.txt(ys(P["mod_back"]+clr/2), zs(48), "header", "cmp", size=2.6)

    s.rect(ys(P["rec_back"]-P["bat_t"]), zs(74), P["bat_t"]*SC, zs(38)-zs(74), "cell")
    s.txt(ys(P["rec_back"]-P["bat_t"]/2), zs(55), "cell", "cmp", size=2.6, rot=-90)
    if HEADER:
        s.rect(ys(P["rec_back"]-P["bat_t"]), zs(62), (P["conn_h"]-clr)*SC, zs(44)-zs(62), "clash")
        s.txt(ys(P["mod_back"]+P["conn_h"]/2), zs(66.5), f"CLASH {n(P['conn_h']-clr)}", "clashtxt", size=2.8)
    s.rect(ys(P["drv_back"]-P["drv_env"]), zs(96), P["drv_env"]*SC, zs(80)-zs(96), "pcb")
    s.txt(ys(P["drv_back"]-P["drv_env"]/2), zs(88), f"driver {n(P['drv_env'])}", "cmp", size=2.5)
    s.rect(ys(P["proto_face"]), zs(32), P["proto_t"]*SC, zs(10)-zs(32), "pcb")
    s.rect(ys(P["proto_face"]-P["chg_t"]+P["proto_t"]), zs(28), (P["chg_t"]-P["proto_t"])*SC, zs(14)-zs(28), "chg")
    s.txt(ys(P["proto_face"]-P["chg_t"]/2), zs(20), f"{P['chg_part']} stack {n(P['chg_t'])}", "cmp", size=2.6)

    lad = bot+9
    s.dimh(ys(0), ys(D), lad+17, n(D), ext_from=bot)
    s.dimh(ys(0), ys(P["front_t"]), lad, n(P["front_t"]), ext_from=bot, flip=True)
    s.dimh(ys(P["front_t"]), ys(P["mod_back"]), lad, n(P["mod_back"]-P["front_t"]), ext_from=bot)
    s.dimh(ys(P["mod_back"]), ys(P["rec_back"]-P["bat_t"]), lad+8.5, n(P["rec_back"]-P["bat_t"]-P["mod_back"]), ext_from=bot)
    s.dimh(ys(P["rec_back"]), ys(D), lad, n(D-P["rec_back"]), ext_from=bot)
    s.txt(ys(D/2), 16, "SECTION A-A  ·  depth axis magnified x5.2", "vlabel")

    cx = 158
    s.txt(cx, 24, "DEPTH BUDGET", "vlabel", "start", 3.2)
    rows = [
        ("front face to module back", P["mod_back"], False),
        ("clear in front of the cell", P["rec_back"]-P["bat_t"]-P["mod_back"], True),
        ("clear in front of proto PCB", P["proto_face"]-P["mod_back"], False),
        (f"...less the {P['chg_part']} stack", P["proto_face"]-P["chg_t"]+P["proto_t"]-P["mod_back"], False),
        ("clear in front of driver PCB", P["drv_back"]-P["drv_t"]-P["mod_back"], False),
        ("interior, on the register face", P["elec_back"]-P["mod_back"], False),
        ("interior, over the recess", P["rec_back"]-P["mod_back"], False),
        ("total depth", D, False),
    ]
    for i, (lab, v, warn) in enumerate(rows):
        y = 30 + i*6.9
        s.txt(cx, y, lab, "note", "start", 2.75)
        s.txt(cx+86, y, n(v), "val"+(" warn" if warn else ""), "end", 3.3)
        s.line(cx, y+2.4, cx+86, y+2.4, "tbrule")
    y0 = 30+len(rows)*6.9+6
    clr = P["rec_back"] - P["bat_t"] - P["mod_back"]
    need = P["conn_h"] + P["bat_t"] + P["mod_back"] + 5.95 + 0.5
    if HEADER:
        s.txt(cx, y0, "THE TIGHT ONE", "vlabel", "start", 3.2)
        body = [f"A mated vertical PH2.0 plug plus a wire bend is",
                f"8-9 mm. Over the boards there is {n(P['proto_face']-P['mod_back'])} and it fits.",
                f"Over the cell there is {n(clr)} and it does not - the",
                f"keep-out overruns the cell face by {n(P['conn_h']-clr)}.",
                "",
                "Three ways out. Which is right depends on where",
                "the header actually is - measure it, see sheet 2:"]
        opts = [
            ("1", ["put the boards in whichever band the header",
                   "lands in, cell in the other. No thickness cost,",
                   "but it moves the driver USB-C to the far wall and",
                   "the charge port out of the board band."]),
            ("2", ["right-angle PH2.0 housing, or desolder the",
                   f"header and lay the eight wires flat. Keeps",
                   f"depth {n(D)}; needs conn_h <= {n(clr-0.5)}."]),
            ("3", [f"set depth = {n(need)} and re-export, which costs",
                   f"+{n(need-D)} mm of thickness."]),
        ]
    else:
        s.txt(cx, y0, "WHERE THE DEPTH GOES", "vlabel", "start", 3.2)
        body = [f"Nothing is plugged into the back of the module:",
                f"the panel's ribbon goes to the driver board's own",
                f"24-pin socket, so the {n(clr)} over the cell is clear.",
                "",
                "The recess is a {0} wide band on the centreline and".format(n(rec_w)),
                "the driver carrier misses it, so the carrier datums",
                f"to the cover's REGISTER face at {n(P['elec_back'])} - not to",
                f"cov_in {n(P['cov_in'])}, which is the skin datum, and not to",
                f"the recess floor's backing at {n(P['rec_back'])}:"]
        opts = [
            ("1", [f"board + tallest part, assumed {n(P['drv_env'])}. Measure it;",
                   "it is the only number holding this sheet up."]),
            ("2", [f"the register face gives {n(P['elec_back']-P['mod_back'])}, less the {n(P['carrier_lift'])} the",
                   f"pads lift the board off it for its solder joints",
                   f"-> {n(P['drv_room'])}, against a measured stack of {n(P['drv_stack'])}:",
                   f"it fits by {n(P['drv_room']-P['drv_stack'])}. Crossing the recess band",
                   f"would cost another {n(P['elec_back']-P['rec_back'])}."]),
            ("3", [f"the cell DOES cross the recess band, so it rides a",
                   f"platform level with the floor's back at {n(P['rec_back'])};",
                   f"it needs {n(P['bat_t'])} of the {n(clr)} in front of that."]),
        ]
    for i, t in enumerate(body):
        s.txt(cx, y0+7+i*3.9, t, "note", "start", 2.65)
    oy2 = y0 + 7 + len(body)*3.9 + 3
    for num, lines in opts:
        s.txt(cx, oy2, num, "val", "start", 2.65)
        for j, ln in enumerate(lines):
            s.txt(cx+5, oy2 + j*3.9, ln, "note", "start", 2.65)
        oy2 += len(lines)*3.9 + 2.6
    s.titleblock(TBX, TBY, 96, 18, "DEPTH STACK-UP", 3, 8, "SEE NOTE")
    return s.render("s3")


# ============================================================ SHEET 4
def sheet4():
    s = mk()
    ox, oy = 16, 24
    fx, fz = views(s, ox, oy)
    s.rect(fx(-W/2), fz(H), W, H, "part", P["corner_r"])
    s.rect(fx(-win_w/2), fz(Zc+win_h/2), win_w, win_h, "cut", 3)
    s.rect(fx(cav_x0), fz(cav_z1), cav_w, cav_h, "hid", P["cav_r"])
    for sx in (-1, 1):
        for sz in (-1, 1):
            s.circ(fx(P["pcb_px"]+sx*cav_w/2), fz(Zc+sz*cav_h/2), 2*P["cav_rel"], "hid")
    pw = P["pan_w"] + 2*P["pan_clr_w"];  ph = P["pan_h"] + 2*P["pan_clr_h"]
    px0 = P["pan_px"] - pw/2;  pz1 = Zc + ph/2
    s.rect(fx(px0), fz(pz1), pw, ph, "hid", P["pan_r"])
    for sx in (-1, 1):
        for sz in (-1, 1):
            s.circ(fx(P["pan_px"]+sx*pw/2), fz(Zc+sz*ph/2), 2*P["pan_rel"], "hid")
    s.rect(fx(px0-P["rib_clr"]), fz(P["rib_cz"]+P["rib_w"]/2), P["rib_clr"], P["rib_w"], "cut")
    s.dimv(fz(Zc-ph/2), fz(P["rib_cz"]-P["rib_w"]/2), fx(px0)-6, n(P["rib_off"]), ext_from=fx(px0))
    s.dimv(fz(P["rib_cz"]+P["rib_w"]/2), fz(P["rib_cz"]-P["rib_w"]/2), fx(px0)-14, n(P["rib_w"]), ext_from=fx(px0-P["rib_clr"]))
    s.dimv(fz(Zc+ph/2), fz(P["rib_cz"]+P["rib_w"]/2), fx(px0)-6, n(P["rib_far"]), ext_from=fx(px0))
    for (sx, sz) in SCR:
        s.circ(fx(sx), fz(sz), P["scr_pilot"], "cut")
    s.rect(fx(P["flash_x"]-P["usb_w"]/2), fz(H), P["usb_w"], H-cav_z1,
           "cut" if FLASH else "hid")
    s.txt(fx(0), fz(H)-14, "FRAME  ·  view on the open back", "vlabel")
    s.dimh(fx(-W/2), fx(W/2), fz(0)+15, n(W), ext_from=fz(0))
    s.dimv(fz(H), fz(0), fx(-W/2)-12, n(H), ext_from=fx(-W/2))
    s.dimh(fx(cav_x0), fx(cav_x1), fz(cav_z1)-4, n(cav_w), ext_from=fz(cav_z1))
    s.dimv(fz(cav_z1), fz(cav_z0), fx(cav_x1)+13, n(cav_h), ext_from=fx(cav_x1))
    s.dimh(fx(-W/2), fx(cav_x0), fz(0)+7, n(cav_x0+W/2), ext_from=fz(cav_z0))
    s.dimh(fx(cav_x1), fx(W/2), fz(0)+7, n(W/2-cav_x1), ext_from=fz(cav_z0))
    if BARE:
        s.dimv(fz(P["scr_cz"]), fz(0), fx(W/2)+13, n(P["scr_cz"]), ext_from=fx(P["scr_cx"]))
        s.dimh(fx(P["scr_cx"]), fx(W/2), fz(0)+22, n(W/2-P["scr_cx"]), ext_from=fz(P["scr_cz"]))
    else:
        s.dimv(fz(P["scr_z2"]), fz(P["scr_z1"]), fx(W/2)+13, n(P["scr_z2"]-P["scr_z1"]), ext_from=fx(P["scr_x"]))
        s.dimv(fz(P["scr_z1"]), fz(P["scr_z0"]), fx(W/2)+13, n(P["scr_z1"]-P["scr_z0"]), ext_from=fx(P["scr_x"]))
        s.dimv(fz(P["scr_z0"]), fz(0), fx(W/2)+13, n(P["scr_z0"]), ext_from=fx(P["scr_x"]))
    s.bal(fx(SCR[-1][0]), fz(SCR[-1][1]), 1, fx(SCR[-1][0])-9, fz(SCR[-1][1])-7)
    s.bal(fx(P["flash_x"]), fz(H-1), 2, fx(P["flash_x"])+18, fz(H)-6)
    s.bal(fx(cav_x0-1.1), fz(Zc+30), 3, fx(cav_x0)-9, fz(Zc+38))

    SC = 7.2
    sx, sy = 130, 34
    ys = lambda y: sx + y*SC
    zz = lambda z: sy + (60-z)*1.45
    s.rect(ys(0), zz(60), P["front_t"]*SC, zz(0)-zz(60), "part"); s.hatch(ys(0), zz(60), P["front_t"]*SC, zz(0)-zz(60))
    s.rect(ys(0), zz(60), P["pcb_face_y"]*SC, zz(46)-zz(60), "part"); s.hatch(ys(0), zz(60), P["pcb_face_y"]*SC, zz(46)-zz(60))
    s.rect(ys(0), zz(14), P["pcb_face_y"]*SC, zz(0)-zz(14), "part"); s.hatch(ys(0), zz(14), P["pcb_face_y"]*SC, zz(0)-zz(14))
    s.rect(ys(P["front_t"]), zz(44), P["pan_t"]*SC, zz(16)-zz(44), "glass")
    s.rect(ys(P["pcb_face_y"]), zz(50), P["pcb_t"]*SC, zz(10)-zz(50), "pcb")
    s.txt(ys(0), zz(60)-9, "SECTION B-B  ·  front lip", "vlabel", "start", 3.0)
    s.dimh(ys(0), ys(P["front_t"]), zz(0)+10, n(P["front_t"]), ext_from=zz(0), flip=True)
    s.dimh(ys(P["front_t"]), ys(P["pcb_face_y"]), zz(0)+10, n(P["pcb_face_y"]-P["front_t"]), ext_from=zz(0))
    s.dimh(ys(P["pcb_face_y"]), ys(P["mod_back"]), zz(0)+10, n(P["pcb_t"]), ext_from=zz(0))
    s.bal(ys(P["front_t"]/2), zz(47), 4, ys(P["front_t"]/2)-9, zz(53))
    s.bal(ys(P["pcb_face_y"]/2), zz(11), 5, ys(P["pcb_face_y"]/2)-9, zz(5))
    s.bal(fx(P["pan_px"]-(P["pan_w"]+2*P["pan_clr_w"])/2-P["rib_clr"]/2), fz(P["rib_cz"]), 6, fx(-W/2)-9, fz(P["rib_cz"]))
    s.bal(fx(P["pan_px"]-(P["pan_w"]+2*P["pan_clr_w"])/2), fz(Zc+(P["pan_h"]+2*P["pan_clr_h"])/2), 7,
          fx(-W/2)-9, fz(Zc+(P["pan_h"]+2*P["pan_clr_h"])/2)+8)

    s.notes(192, 24, [
        (1, f"4 x dia {n(P['ins_d'])} bores, {n(P['ins_l']+1)} deep from the back face, for {n(P['ins_d'])}-bore heat-set inserts. Melt them in flush; the screws come down through the cover into them"
            if INSERT else
            f"3 x dia {n(P['scr_pilot'])} pilot holes, 8 deep, drilled from the back face"),
        (2, f"flash port, {n(P['usb_w'])} wide, through the {n(P['wall'])} top wall"
            if FLASH else
            f"blind pocket {n(P['usb_w'])} wide for the driver board's own USB-C; the "
            f"top wall stays solid, {n(P['flash_skin'])} of skin outboard of the jack"),
        (3, f"cavity {n(cav_w)} x {n(cav_h)}, corners R{n(P['cav_r'])} - inside the 1.707 limit for a sharp PCB corner in a {n(P['mod_clr']/2)} clearance pocket, so no corner relief is needed here"),
        (4, "panel recess - the glass stands 1.05 proud of the PCB, so the seat is stepped"),
        (5, "PCB pocket"),
        (6, f"ribbon relief {n(P['rib_clr'])} out x {n(P['rib_w'])} along the thick-bezel edge - a LONG-AXIS edge - {n(P['rib_off'])} from one end, {n(P['rib_far'])} from the other, {n(P['rib_dep'])} past the glass back face. A slot rather than a local pocket because the ribbon runs ALONG this edge; it also sets the frame width"),
        (7, f"corner relief R{n(P['pan_rel'])} at all four GLASS pocket corners, so the glass's sharp corners seat"),
    ], cw=36)
    s.notes(192, 145, [], title="LIP OVERLAP ON THE GLASS")
    for i, t in enumerate([
        f"top / bottom   {n((P['pan_h']-win_h)/2)}",
        f"ribbon side    {n(P['pan_w']/2-P['pan_px']-win_w/2)}",
        f"opposite side  {n(P['pan_w']/2+P['pan_px']-win_w/2)}",
    ]):
        s.txt(192, 152 + i*3.8, t, "note", "start", 2.7)

    s.notes(16, 149, [], title="THE MODULE, AND THE RIBBON ROUTE")
    for i, t in enumerate([
        f"glass {n(P['pan_w'])} x {n(P['pan_h'])}, sharp corners. Dead border",
        f"{n(P['bez_thin'])} on three sides, {n(P['bez_thick'])} on the ribbon side.",
        f"Pocket margin {n(2*P['pan_clr_w'])} on the width, {n(2*P['pan_clr_h'])} on the height.",
        "Seen from the rear, the ribbon leaves",
        "the thick-bezel edge - a LONG-AXIS edge",
        "- folds back behind the glass, turns 90",
        "deg to run ALONG that edge, then 90 deg",
        "back out to the header. That run is why",
        f"the relief is a {n(P['rib_w'])} slot, not a pocket.",
    ]):
        s.txt(16, 155 + i*3.6, t, "note", "start", 2.7)

    # ---- DETAIL C : one pocket corner, 6:1
    DC = 6.0
    ox0, oy0 = 106.0, 166.0
    cu = lambda u: ox0 + u*DC
    cv = lambda v: oy0 - v*DC
    U0, U1, V0, V1 = -2.2, 1.4, -2.2, 1.4
    s.txt(88, 152, "DETAIL C  ·  pocket corner  ·  6:1", "vlabel", "start", 3.2)
    s.rect(cu(0), cv(V1), (U1-0)*DC, (V1-V0)*DC, "part")
    s.rect(cu(U0), cv(V1), (0-U0)*DC, (V1-0)*DC, "part")
    r = P["pan_r"]
    s.path(f"M{cu(U0):.2f},{cv(0):.2f} L{cu(-r):.2f},{cv(0):.2f} "
           f"A{r*DC:.2f},{r*DC:.2f} 0 0 0 {cu(0):.2f},{cv(-r):.2f} "
           f"L{cu(0):.2f},{cv(V0):.2f}", "cut")
    s.circ(cu(0), cv(0), 2*P["pan_rel"]*DC, "cut")
    gw, gh = P["pan_clr_w"], P["pan_clr_h"]
    s.rect(cu(U0), cv(-gh), (-gw-U0)*DC, (-gh-V0)*DC, "glass")
    s.txt(cu(U0*0.60), cv(V0*0.60), "glass", "cmp", size=2.5)
    s.leader(cu(P["pan_rel"]*0.72), cv(P["pan_rel"]*0.72), cu(U1)+1, cv(V1)-2.5,
             f"R{n(P['pan_rel'])}", "start")
    import textwrap as _tw
    _lines = []
    for para in [
        "Relief is centred ON the theoretical sharp corner, so it "
        "undercuts equally in both axes.",
        "All four corners are identical.",
    ]:
        _lines += _tw.wrap(para, 22) + [""]
    for i, t in enumerate(_lines):
        s.txt(124, 158 + i*3.8, t, "note", "start", 2.6)
    s.titleblock(TBX, TBY, 96, 18, "FRAME", 4, 8, "1:1")
    return s.render("s4")


# ============================================================ SHEET 5
def sheet5():
    s = mk()
    ox, oy = 22, 14
    fx, fz = views(s, ox, oy)
    s.rect(fx(-W/2), fz(H), W, H, "part", P["corner_r"])
    s.rect(fx(cav_x0+0.85), fz(cav_z1-0.85), cav_w, cav_h, "hid", P["cav_r"])
    # the stand recess, seen from inside the cover: it is a blind pocket in the
    # BACK face, so from here only its footprint and the pin sockets show
    s.rect(fx(-rec_w/2), fz(rec_top), rec_w, rec_top-rec_z0, "hid", 1)
    # the register extension: the plate that floors the shallow end of the pocket.
    # It stops short of the bottom edge on purpose - see note 1.
    s.rect(fx(-P["stand_reg_w"]/2), fz(P["shl_z0"]+0.05),
           P["stand_reg_w"], (P["shl_z0"]+0.05)-P["reg_ext_z0"], "boss")
    for sx_ in (-1, 1):   # the ears, inside the pocket, and their sockets
        s.rect(fx(sx_*P["ear_x0"] - (P["ear_w"] if sx_ < 0 else 0)),
               fz(piv_z + P["ear_len"]/2), P["ear_w"], P["ear_len"], "boss")
        s.circ(fx(sx_*(P["ear_x0"] + P["ear_w"]/2)), fz(piv_z),
               P["pin_d"]+P["pin_fit"], "cut")
    for (sx, sz) in SCR:
        s.circ(fx(sx), fz(sz), P["scr_head"], "cut")
    s.rect(fx(cav_x0+0.3), fz(P["bat_cz"]+P["bat_h"]/2+P["bat_clr"]+P["bat_fence"]),
           P["bat_cx"]+P["bat_w"]/2+P["bat_clr"]+P["bat_fence"]-(cav_x0+0.3),
           P["bat_h"]+2*P["bat_clr"]+2*P["bat_fence"], "plat", 1)
    if BARE:
        if PERF:
            s.rect(fx(P["perf_cx"]-P["perf_w"]/2), fz(P["perf_cz"]+P["perf_h"]/2),
                   P["perf_w"], P["perf_h"], "pcb", 1)
            for sx_ in (-1, 1):
                for sz in (-1, 1):
                    s.circ(fx(P["perf_cx"]+sx_*(P["perf_w"]/2-2.5)),
                           fz(P["perf_cz"]+sz*(P["perf_h"]/2-2.5)), 4.0, "boss")
        # board first, then the posts on top of it: they are the feature this
        # sheet is called on to show, and the board's fill would bury them
        s.rect(fx(P["chg_x_c"]-P["chg_w"]/2), fz(P["chg_z"]+P["chg_h"]/2),
               P["chg_w"], P["chg_h"], "chg", 1)
        for sx_ in (-1, 1):
            for sz in (-1, 1):
                cx_, cz_ = fx(P["chg_x_c"]+sx_*P["chg_hx"]/2), fz(P["chg_z"]+sz*P["chg_hz"]/2)
                s.circ(cx_, cz_, P["chg_boss_d"], "boss")
                s.circ(cx_, cz_, P["chg_ins_d"], "cut")
        # fridge magnet bosses, over the boards so the +X one is not buried by the
        # charger's footprint.  The pocket inside each is blind in the BACK face.
        if MAGS:
            for mx, mz in ((P["mag_x"], P["mag_z0"]), (-P["mag_x"], P["mag_z1"])):
                s.circ(fx(mx), fz(mz), P["mag_bd"], "boss")
                s.circ(fx(mx), fz(mz), P["mag_bore"], "hid")
        else:
            # glued onto the OTHER face - drawn through so the positions are on
            # a sheet, since nothing is cut for them
            for mx, mz in ((P["mag_x"], P["mag_z0"]), (-P["mag_x"], P["mag_z1"])):
                s.circ(fx(mx), fz(mz), P["mag_d"], "hid")
    else:
        for sz in (-1, 1):
            s.circ(fx(P["proto_cx"]), fz(P["proto_cz"]+sz*P["proto_hole_sp"]/2), 6.5, "boss")
        for sx_ in (-1, 1):
            for sz in (-1, 1):
                s.circ(fx(P["proto_cx"]+sx_*(P["proto_w"]/2-4)), fz(P["proto_cz"]+sz*(P["proto_h"]/2-4)), 6.0, "boss")
    if CARRIER:
        # the carrier's footprint and the four pads that carry it - there are no
        # printed rails when the driver rides a carrier
        s.rect(fx(P["carrier_cx"]-P["carrier_w"]/2), fz(P["carrier_cz"]+P["carrier_h"]/2),
               P["carrier_w"], P["carrier_h"], "hid", 1.0)
        for sx_ in (-1, 1):
            for sz in (-1, 1):
                cx_ = fx(P["carrier_cx"]+sx_*P["carrier_hx"]/2)
                cz_ = fz(P["carrier_cz"]+sz*P["carrier_hz"]/2)
                s.circ(cx_, cz_, P["carrier_pad"], "boss")
                s.circ(cx_, cz_, P["carrier_hole"]-P["carrier_peg"], "cut")
    else:
        for sx_ in (-1, 1):
            s.rect(fx(P["drv_cx"]+sx_*(P["drv_w"]/2+P["drv_clr"]+0.3)-1.5), fz(P["drv_cz"]+(P["drv_h"]-1)/2), 3.0, P["drv_h"]-1, "boss")
    pw, ph = port_opening(s, fx, fz)
    if not BARE:
        for sz in (-1, 1):
            z = Zc+sz*(cav_h/2-P["rib_inset"]-P["rib_pad"]/2)
            s.rect(fx(P["bat_cx"]-(P["bat_w"]-2)/2), fz(z+P["rib_pad"]/2), P["bat_w"]-2, P["rib_pad"], "pad", 0.8)

    s.txt(fx(0), fz(H)-8, "BACK COVER  ·  inner face", "vlabel")
    s.dimv(fz(piv_z), fz(0), fx(-W/2)-12, n(piv_z), ext_from=fx(-W/2))
    s.dimh(fx(-W/2), fx(W/2), fz(0)+15, n(W), ext_from=fz(0))
    s.dimh(fx(P["chg_x_c"]), fx(W/2), fz(0)+8, n(W/2-P["chg_x_c"]), ext_from=fz(P["chg_z"]))
    s.dimv(fz(P["chg_z"]), fz(0), fx(W/2)+7, n(P["chg_z"]), ext_from=fx(P["chg_x_c"]))
    s.bal(fx(rec_w/2), fz(piv_z), 1, fx(rec_w/2)+10, fz(piv_z)-8)
    s.bal(fx(P["stand_reg_w"]/2), fz(P["reg_ext_z0"]+1.0), 8,
          fx(P["stand_reg_w"]/2)+14, fz(P["reg_ext_z0"])-4)
    s.bal(fx(-P["mag_x"]), fz(P["mag_z1"]), 9, fx(-P["mag_x"])-14, fz(P["mag_z1"])-8)
    s.bal(fx(P["chg_x_c"]), fz(P["chg_z"]+P["chg_hz"]/2), 2, fx(P["chg_x_c"])+12, fz(P["chg_z"])+6)
    if CARRIER:
        s.bal(fx(P["carrier_cx"]+P["carrier_hx"]/2), fz(P["carrier_cz"]-P["carrier_hz"]/2), 3,
              fx(P["carrier_cx"]+P["carrier_w"]/2)+11, fz(P["carrier_cz"]-P["carrier_hz"]/2)-6)
    else:
        s.bal(fx(P["drv_cx"]+P["drv_w"]/2+2), fz(P["drv_cz"]), 3, fx(P["drv_cx"]+P["drv_w"]/2+2)+9, fz(P["drv_cz"])-6)
    s.bal(fx(P["ucb_x"]), fz(P["ucb_z"]+ph/2), 4, fx(P["ucb_x"])-13, fz(P["ucb_z"])-9)
    s.bal(fx(P["bat_cx"]-8), fz(P["bat_cz"]+P["bat_h"]/2+1), 5, fx(P["bat_cx"]-8)-9, fz(P["bat_cz"]+P["bat_h"]/2+9))
    if BARE and PERF:
        s.bal(fx(P["perf_cx"]), fz(P["perf_cz"]), 7, fx(P["perf_cx"])-14, fz(P["perf_cz"])-8)
    s.bal(fx(SCR[1][0]), fz(SCR[1][1]), 6, fx(SCR[1][0])-14, fz(SCR[1][1])-6) if BARE else \
        s.bal(fx(P["bat_cx"]), fz(cav_z0+4), 6, fx(P["bat_cx"])+13, fz(cav_z0+4)-6)

    s.notes(150, 22, [
        (1, f"stand recess in the BACK face, hidden here because it does not break through: {n(rec_w)} wide x {n(P['rec_dep'])} deep, stepping to {n(P['rec_shl'])} below z {n(P['shl_z0'])}. Pin sockets are on EARS inside it, not bored through its walls - sheet 6"),
        (2, f"four dia {n(P['chg_boss_d'])} posts under the {P['chg_part']} charger, {n(P['chg_hx'])} x {n(P['chg_hz'])} centres, {n(P['chg_stand'])} off the register face, bored dia {n(P['chg_ins_d'])} x {n(P['chg_bore'])} for M2 inserts. BLIND, {n(P['chg_skin'])} of skin. Centres MEASURED off the vendor STEP - 0.1 in in from each edge of the 31.75 x 25.40 PCB"
            if BARE else
            f"2 x M2.5 posts, {n(P['proto_hole_sp'])} apart, plus four corner pads"),
        (3, f"four carrier mounts: a dia {n(P['carrier_pad'])} PAD {n(P['carrier_lift'])} tall - the air the solder joints under the board need - carrying a dia {n(P['carrier_hole']-P['carrier_peg'])} PEG that locates it through its hole"
            if CARRIER else
            "driver-board rails - the board slides down from the top, stop at the bottom"),
        (4, f"USB-C charge port, opening {n(P['snap_w']+2*P['snap_c'])} x {n(P['snap_h']+2*P['snap_ch'])} at x {n(P['ucb_x'])} z {n(P['ucb_z'])}: a snap-in pigtail, nothing printed around it. The height gets the bigger clearance - it is the tight axis"
            if SNAP else
            "USB-C breakout rails; the port opening is through the skin below them"),
        (5, f"cell platform at depth {n(P['rec_back'])}, level with the back of the recess floor so the cell does not straddle the step, {n(P['bat_fence'])} fence"),
        *([(7, f"divider / wiring perfboard {n(P['perf_w'])} x {n(P['perf_h'])} - 11 x 4 holes of 0.1 inch strip - on four standoff pads. The band above the driver board is {n(P['cav_z1']-P['drv_z1'])} tall")]
          if (BARE and PERF) else []),
        (6, "the four corner screw holes, counterbored" if BARE else "module retention pad"),
        (9, f"two dia {n(P['mag_bore'])} x {n(P['mag_dep'])} BLIND pockets for dia {n(P['mag_d'])} x {n(P['mag_t'])} discs, each on a dia {n(P['mag_bd'])} boss {n(P['mag_boss'])} proud, leaving {n(P['mag_floor'])} in front. MIRRORED at x +/-{n(P['mag_x'])} so the pair's centroid is on the centreline; offset, they hang it crooked. The two z differ - the -X half is carrier board to z {n(P['carrier_z1'])}"
            if MAGS else
            f"NOTHING IS CUT HERE. The two dia {n(P['mag_d'])} x {n(P['mag_t'])} discs are GLUED onto the OUTER back face at these positions, shown through - the USB-C pigtail's flange stands 2.00 proud and is the rearmost thing on the case, so a sunk disc could not reach the steel. A 2 mm disc glued on is exactly as proud as the flange. MIRRORED at x +/-{n(P['mag_x'])} so the pair's centroid is on the centreline; offset, they hang it crooked. The two z differ - the -X half is carrier board to z {n(P['carrier_z1'])}"),
        (8, f"the register extension, {n(P['stand_reg_w'])} wide, FLOORS the shallow end of the recess. It plugs a frame relief {n(P['reg_fit'])} larger, so it STOPS at z {n(P['reg_ext_z0'])} - clear of the {n(P['chf_bite'])} the rear chamfer takes"),
    ], cw=50)
    s.titleblock(TBX, TBY, 96, 18, "BACK COVER", 5, 8, "1:1")
    return s.render("s5")


# ============================================================ SHEET 6
def sheet6():
    """LEG & PIVOT.  Three views: the leg flat, the pivot in section, and the pin
    socket across the pocket.  The pocket is a plain blind hollow - no detent, no
    seat, no lip across its mouth - so the floor in view B is a flat face and the
    only things standing in it are the two ears."""
    s = mk()
    bore = P["pin_d"]+P["pin_fit"]
    hw, hz = P["leg_w"]/2, P["heel_z"]
    fr, L  = P["foot_r"], P["leg_len"]

    # ---------------------------------------------- A: the leg, printed flat
    lx, ly = 30, 32
    s.txt(lx, ly-hz-10, "A  ·  LEG, printed flat", "vlabel")
    s.path(f'M{lx-hw:.2f},{ly-hz:.2f} L{lx+hw:.2f},{ly-hz:.2f} '
           f'L{lx+hw:.2f},{ly+L-fr:.2f} '
           f'A{fr},{fr} 0 0 1 {lx+hw-fr:.2f},{ly+L:.2f} '
           f'L{lx-hw+fr:.2f},{ly+L:.2f} '
           f'A{fr},{fr} 0 0 1 {lx-hw:.2f},{ly+L-fr:.2f} Z', "part")
    s.line(lx-hw, ly+(piv_z-P["shl_z0"]), lx+hw, ly+(piv_z-P["shl_z0"]), "hid")
    s.circ(lx, ly, bore, "cut")
    s.line(lx, ly-hz-6, lx, ly+L+8, "cl")
    s.line(lx-hw-6, ly, lx+hw+6, ly, "cl")
    s.dimv(ly, ly+L, lx-hw-11, n(L), ext_from=lx)
    s.dimv(ly-hz, ly, lx+hw+9, n(hz), ext_from=lx)
    s.dimh(lx-hw, lx+hw, ly-hz-6, n(P["leg_w"]), ext_from=ly-hz)
    s.bal(lx+P["pin_d"]/2, ly, 3, lx+hw+9, ly+10)
    s.bal(lx, ly+L-1, 4, lx-hw-9, ly+L-4)
    s.bal(lx+hw, ly+(piv_z-P["shl_z0"]), 6, lx+hw+10, ly+(piv_z-P["shl_z0"])+7)

    # ------------------------------------- B: section at the pivot, 4:1
    SC6 = 4.0
    bx, by = 104, 56
    sx = lambda y: bx + (y - piv_y)*SC6
    sy = lambda z: by - (z - piv_z)*SC6
    D6 = P["depth"]
    zlo, zhi = piv_z - 7.0, piv_z + 8.0
    s.txt(bx+6, 16, "B  ·  SECTION AT THE PIVOT  ·  4:1", "vlabel")
    s.txt(bx+6, 20.5, "leg DEPLOYED solid, FOLDED hidden", "note", size=2.6)
    s.rect(sx(P["rec_back"]), sy(rec_top), (rec_y0-P["rec_back"])*SC6,
           (rec_top-zlo)*SC6, "part")
    s.hatch(sx(P["rec_back"]), sy(rec_top), (rec_y0-P["rec_back"])*SC6,
            (rec_top-zlo)*SC6)
    s.rect(sx(P["rec_back"]), sy(zhi), (D6-P["rec_back"])*SC6,
           (zhi-rec_top)*SC6, "part")
    s.hatch(sx(P["rec_back"]), sy(zhi), (D6-P["rec_back"])*SC6, (zhi-rec_top)*SC6)
    s.line(sx(D6), sy(zhi), sx(D6), sy(zlo), "edge")
    s.txt(sx(D6)+3, sy(zhi)+4, "back face", "note", "start", 2.5)
    t2 = P["leg_t"]/2
    zl_flat = (piv_h - math.cos(math.radians(DEP))*t2) / math.sin(math.radians(DEP))
    yl_heel = (math.sin(math.radians(DEP))*hz - piv_h) / math.cos(math.radians(DEP))
    poly = [(t2, hz), (t2, -5.0), (-t2, -5.0), (-t2, zl_flat), (yl_heel, hz)]
    def place(yl, zl, th):
        t = math.radians(th)
        return (piv_y + yl*math.cos(t) - zl*math.sin(t),
                piv_z + yl*math.sin(t) + zl*math.cos(t))
    for th, cls in ((0.0, "hid"), (DEP, "part")):
        pts = [place(a, b, th) for a, b in poly]
        s.path("M"+" L".join(f"{sx(y):.2f},{sy(z):.2f}" for y, z in pts)+" Z", cls)
    s.circ(sx(piv_y), sy(piv_z), bore*SC6, "cut")
    s.line(sx(P["rec_back"])-4, sy(piv_z), sx(D6)+14, sy(piv_z), "cl")
    s.line(sx(piv_y), sy(zlo)-4, sx(piv_y), sy(zhi)+4, "cl")
    RA = 24
    s.path(f'M{sx(piv_y):.2f},{sy(piv_z)+RA:.2f} '
           f'A{RA},{RA} 0 0 0 {sx(piv_y)+RA*math.sin(math.radians(DEP)):.2f},'
           f'{sy(piv_z)+RA*math.cos(math.radians(DEP)):.2f}', "dim")
    s.txt(sx(piv_y)+(RA+4)*math.sin(math.radians(DEP/2)),
          sy(piv_z)+(RA+8)*math.cos(math.radians(DEP/2)), f"{n(DEP)} deg",
          "dimtxt", "start", 3.2)
    s.dimh(sx(rec_y0), sx(piv_y), sy(zlo)+10, n(piv_h), ext_from=sy(piv_z))
    s.dimh(sx(rec_y0), sx(D6), sy(zlo)+19, n(P["rec_dep"]), ext_from=sy(zlo)+2)
    s.bal(sx(rec_y0), sy(piv_z-2.2), 5, sx(rec_y0)-11, sy(zlo)-1)

    # ---------------------------- C: the pin socket, transverse, 3:1
    SCc = 3.0
    cx, cy = 104, 138
    tx = lambda x: cx + x*SCc
    ty = lambda y: cy - (y - piv_y)*SCc
    s.txt(cx+10, cy-24, "C  ·  PIN SOCKET  ·  transverse at z "+n(piv_z)+"  ·  3:1", "vlabel")
    wallx = P["rec_wall"] + 3.0
    for sgn in (-1, 1):
        # the pocket wall, outboard
        x0 = sgn*rec_w/2
        xa = min(x0, x0+sgn*wallx)
        s.rect(tx(xa), ty(P["depth"]), wallx*SCc, (P["depth"]-P["rec_back"])*SCc, "part")
        s.hatch(tx(xa), ty(P["depth"]), wallx*SCc, (P["depth"]-P["rec_back"])*SCc)
        # the EAR, inboard of it, and its C-socket
        xe = sgn*P["ear_x0"] - (P["ear_w"] if sgn < 0 else 0)
        s.rect(tx(xe), ty(P["depth"]), P["ear_w"]*SCc, (P["depth"]-P["rec_y0"])*SCc, "part")
        s.hatch(tx(xe), ty(P["depth"]), P["ear_w"]*SCc, (P["depth"]-P["rec_y0"])*SCc)
        s.rect(tx(xe), ty(piv_y+bore/2), P["ear_w"]*SCc, bore*SCc, "cut")
        s.rect(tx(xe), ty(P["depth"]), P["ear_w"]*SCc,
               (P["depth"]-piv_y-bore*P["ear_mouth"]/2)*SCc, "cut")
    # the pocket floor, which the boss provides
    s.rect(tx(-rec_w/2), ty(P["rec_y0"]), rec_w*SCc, (P["rec_y0"]-P["rec_back"])*SCc, "part")
    s.hatch(tx(-rec_w/2), ty(P["rec_y0"]), rec_w*SCc, (P["rec_y0"]-P["rec_back"])*SCc)
    s.rect(tx(-hw), ty(piv_y+t2), P["leg_w"]*SCc, P["leg_t"]*SCc, "hid")
    # the pin itself, in section: a bar spanning both sockets
    s.rect(tx(-P["pin_len"]/2), ty(piv_y+P["pin_d"]/2), P["pin_len"]*SCc,
           P["pin_d"]*SCc, "res")
    s.txt(tx(0), ty(piv_y)+1.0, f"pin dia {n(P['pin_d'])} x {n(P['pin_len'])}", "cmp", size=2.6)
    s.line(tx(-rec_w/2-wallx-2), ty(piv_y), tx(rec_w/2+wallx+2), ty(piv_y), "cl")
    s.dimh(tx(-rec_w/2), tx(rec_w/2), ty(P["rec_back"])+9, n(rec_w),
           ext_from=ty(P["rec_back"]))
    s.dimh(tx(-hw), tx(hw), ty(P["rec_back"])+17, n(P["leg_w"]), ext_from=ty(P["rec_back"]))
    s.bal(tx(P["ear_x0"]+P["ear_w"]/2), ty(piv_y-0.8), 1, tx(rec_w/2+wallx)-2, ty(piv_y)-13)
    s.bal(tx(-hw+1), ty(piv_y+t2), 2, tx(-rec_w/2-wallx-5), ty(piv_y)-11)

    s.notes(178, 18, [
        (1, f"pin socket through each EAR, {n(P['ear_w'])} thick, standing inside the pocket. Bore dia {n(bore)}, mouth {n(bore*P['ear_mouth'])} across: the pin snaps past the lip and is then retained by it. On ears, not bored through the pocket walls - outward, the mouth could only be reached from outside, which breaks the back face"),
        (2, f"leg {n(P['leg_w'])} wide, set by the pocket: {n(rec_w)} less two {n(P['ear_w'])} ears and {n(P['rec_clr'])} each. Off the ears, {n(P['finger_g'])} is open either side the whole length - the finger access"),
        (3, f"dia {n(bore)} axle hole through the leg"),
        (4, f"foot R{n(P['foot_r'])} in plan"),
        (5, f"THE STOP: at {n(DEP)} deg a {n(3.07)} x {n(P['leg_w'])} flat on the heel lands on the recess floor. Load runs leg - heel - cover in COMPRESSION. The pocket is otherwise a plain blind hollow - no detent seat, no track, nothing bridging its mouth - and the leg swings free between the poses"),
        (6, f"the taper is ONE-SIDED and finishes at z {n(P['shl_z0'])}: {n(P['leg_t'])} above, {n(P['leg_tf'])} below"),
    ], cw=42)
    s.titleblock(TBX, TBY, 96, 18, "LEG & PIVOT", 6, 8, "SEE VIEWS")
    return s.render("s6")


# ============================================================ SHEET 7
def sheet7():
    s = mk()
    lean = P["lean"]                      # DERIVED in the model; consumed here
    a = math.radians(lean)
    py = D-P["rear_chf"]
    SC = 1.05
    gx, gy = 46, 140

    def wf(y, z):
        dy, dz = y-py, z
        return gx+(dy*math.cos(a)+dz*math.sin(a))*SC, gy-(-dy*math.sin(a)+dz*math.cos(a))*SC

    s.line(gx-34, gy, gx+112, gy, "table")
    for k in range(-32, 112, 5):
        s.line(gx+k, gy, gx+k-3.4, gy+3.4, "hl")
    pts = [wf(0, 0), wf(0, H), wf(D, H), wf(D, 0)]
    s.path("M"+" L".join(f"{x:.2f},{y:.2f}" for x, y in pts)+" Z", "part")
    p0, p1 = wf(0, cav_z0), wf(0, cav_z1)
    s.line(p0[0], p0[1], p1[0], p1[1], "inkline")

    pv = wf(piv_y, piv_z)
    ft = wf(piv_y + P["leg_len"]*math.sin(math.radians(DEP)),
            piv_z - P["leg_len"]*math.cos(math.radians(DEP)))
    fd = wf(piv_y, P["foot_z"])                     # the folded foot tip
    s.line(pv[0], pv[1], fd[0], fd[1], "hid")       # the leg, folded
    s.line(pv[0], pv[1], ft[0], ft[1], "leg")       # ... and deployed
    s.circ(pv[0], pv[1], 3, "cut")
    ce = wf(py, 0)
    cm = wf(11.0, Zc)
    s.circ(cm[0], cm[1], 3.6, "com")
    s.line(cm[0], cm[1], cm[0], gy, "cl")

    s.bal(pv[0], pv[1], 1, pv[0]+11, pv[1]-9)
    s.bal((pv[0]+fd[0])/2, (pv[1]+fd[1])/2, 2, pv[0]+13, pv[1]+9)
    s.bal(ft[0]-2, ft[1]-2, 3, ft[0]+2, ft[1]-11)
    s.bal(ce[0], ce[1]-1.5, 4, ce[0]-12, ce[1]-11)
    s.bal(cm[0], cm[1], 5, cm[0]-15, cm[1]+9)

    s.line(gx, gy, gx, gy-72, "cl")
    s.path(f'M{gx:.2f},{gy-64:.2f} A64,64 0 0 1 {gx+64*math.sin(a):.2f},{gy-64*math.cos(a):.2f}', "dim")
    s.txt(gx+70*math.sin(a/2)+2, gy-70*math.cos(a/2)-2, f"{lean:.1f} deg", "dimtxt", "start", 3.4)
    s.dimh(gx, ft[0], gy+13, n((ft[0]-gx)/SC), ext_from=gy)
    s.dimh(gx, cm[0], gy+23, n((cm[0]-gx)/SC), ext_from=gy)
    s.txt(gx+3, gy+31, "footprint / CoM offset, both behind the contact edge", "note", "start", 2.6)
    s.txt(gx+20, 16, "SIDE ELEVATION  ·  PORTRAIT  ·  leg deployed and folded", "vlabel", "start", 3.2)

    s.notes(168, 22, [
        (1, f"hinge pin, z {n(piv_z)} and depth {n(piv_y)} - that depth is {n(P['leg_t']/2)} below the back face, which is what makes the folded leg flush"),
        (2, f"the leg folded: it reaches down to z {n(P['foot_z'])}, and the back chamfer ends at {n(P['rear_chf'])}, so nothing overhangs the bottom edge"),
        (3, f"foot deployed. Leg {n(P['leg_len'])} long, hard stop at {n(DEP)} deg on the heel's flat - see sheet 6"),
        (4, "contact edge - the rear edge of the flat bottom, brought forward 2 by the back chamfer. This, not the front edge, is what the frame leans on"),
        (5, "estimated centre of mass. It must sit behind the contact edge or the frame simply falls flat onto its face"),
    ], cw=42)
    y = 100
    s.txt(168, y, "WHAT SETS THE STANCE", "vlabel", "start", 3.2)
    for i, t in enumerate([
        f"The leg is a LEVER. At {n(DEP)} deg the heel on the far",
        "side of the pin reaches the recess floor, so the",
        "stop is a face in compression rather than the",
        "hinge taking a moment.",
        "",
        f"Keeping the swing under 90 deg is what lets the",
        "heel land ON the floor plane instead of rotating",
        "past it, so dep_ang is bounded above by that and",
        "below by the lean the desk needs.",
        "",
        "dep_ang sets the lean; leg_len the footprint.",
        "The two do not interact.",
    ]):
        s.txt(168, y+7+i*4.0, t, "note", "start", 2.7)
    s.txt(168, y+7+12*4.0+5,
          f"lean {lean:.1f} deg   ·   footprint {n(P['footprint'])}", "val", "start", 4.2)
    s.titleblock(TBX, TBY, 96, 18, "STAND KINEMATICS", 7, 8, "1:1.05")
    return s.render("s7")


# ============================================================ SHEET 8
def sheet8():
    s = mk(268, 232)

    def box(x, y, w, h, title, sub=None):
        s.rect(x, y, w, h, "part", 1.5)
        s.txt(x + w/2, y + 7.0, title, "cmp", size=3.3)
        if sub:
            s.txt(x + w/2, y + 11.4, sub, "cmpsub", size=2.6)

    def pin(x, y, label, anchor="start", dx=2.0, up=False):
        s.circ(x, y, 1.6, "cut")
        s.txt(x + (dx if anchor == "start" else -dx), y + (-2.6 if up else 1.0),
              label, "note", anchor, 2.6)

    def wire(pts):
        s.path("M" + " L".join(f"{a:.2f},{b:.2f}" for a, b in pts), "wire")

    box(14, 38, 40, 28, "USB-C", "breakout")
    box(80, 30, 58, 54, P["chg_part"], "charger + power path")
    box(80, 108, 58, 26, "1S LiPo  ·  694449", "2000 mAh, salvaged")
    box(170, 38, 58, 46, "Waveshare", "ESP32 driver board")

    pin(54, 48, "VBUS");            pin(80, 48, "VBUS", "end")
    pin(54, 58, "GND");             pin(80, 58, "GND", "end")
    pin(80, 70, "BATT", "end")
    pin(138, 48, "LOAD");            pin(170, 48, "5V", "end")
    pin(138, 70, "GND");            pin(170, 60, "GND", "end")
    pin(170, 72, "GPIO 32-39", "end")
    pin(80, 80, "TH", "end")
    pin(98, 108, "+ red", up=True);  pin(114, 134, "- black", "start", 2.4)
    pin(126, 108, "NTC", "start", 2.4, up=True)

    wire([(54, 48), (80, 48)]);     s.txt(67, 45.6, "5 V", "dimtxt", "middle", 2.7)
    wire([(54, 58), (80, 58)])
    wire([(80, 70), (66, 70), (66, 98), (98, 98), (98, 108)])
    # yellow NTC leg back to the charger's TS pin
    s.path("M126,108 L126,94 L60,94 L60,80 L80,80", "wire ntc")
    s.txt(93, 92.4, "yellow  ·  10k NTC", "dimtxt", "middle", 2.6)
    wire([(138, 48), (170, 48)]);   s.txt(152, 45.6, "3.0-4.5 V", "dimtxt", "middle", 2.7)
    wire([(138, 70), (150, 70), (150, 60), (170, 60)])
    # divider off the 5 V net
    s.rect(159, 88, 6, 11, "res");  s.txt(168, 94.6, "100k", "note", "start", 2.6)
    s.rect(159, 107, 6, 11, "res"); s.txt(168, 113.6, "100k", "note", "start", 2.6)
    wire([(162, 48), (162, 88)])
    wire([(162, 99), (162, 107)])
    wire([(162, 103), (166, 103), (166, 72), (170, 72)])
    wire([(162, 118), (162, 142)])
    # ground bus
    wire([(80, 58), (56, 58), (56, 142), (162, 142)])
    wire([(114, 134), (114, 142)])
    s.line(108, 142, 120, 142, "wire")
    s.line(110.5, 145, 117.5, 145, "edge")
    s.line(113, 148, 115, 148, "edge")
    s.txt(114, 153, "GND", "note", "middle", 2.6)

    s.bal(67, 48, 1, 40, 24)
    s.bal(109, 30, 2, 109, 18)
    s.bal(152, 48, 3, 152, 22)
    s.bal(162, 103, 4, 144, 103)
    s.bal(80, 80, 6, 40, 80)
    s.bal(170, 48, 5, 200, 22)

    s.txt(120, 12, "POWER WIRING  ·  charge and run from one cell", "vlabel")

    s.notes(14, 164, [
        (1, "USB-C breakout needs 5.1k from CC1 and CC2 to GND or a USB-C source will never turn its 5 V on. VBUS and GND only, no data"),
        (2, "charge current: Adafruit's pinout page says it ships at 500 mA, the product page says 1 A - CHECK THE BOARD. 1 A is 0.5C for this cell and is what you want. Solar capability is input voltage regulation and is inert on USB"),
        (6, "THREE WIRES, all three verified on this pack: red positive to black, and yellow-to-black 10k at room temperature - an NTC. Cut the TH jumper and wire yellow to TH; the charger then refuses to charge outside roughly 0-45 C. The pack carries its own protection PCB at the tab end"),
    ], cw=62)
    s.notes(142, 164, [
        (3, "LOAD is 4.5 V max - from the input when plugged in, from the cell otherwise. The 5V pin takes 3.6-5.5 V and browns out near 3.6 V"),
        (4, "divider must land on ADC1 (GPIO 32-39) - ADC2 is dead while WiFi is on. Below 3.6 V firmware MUST deep-sleep for good, or the cell gets dragged to its protection cut"),
        (5, "PWR / CHRG / FAULT LEDs onboard; S1 and S2 pads mirror them. /CE pulled high disables charging"),
    ], cw=58, title=" ")
    s.titleblock(268 - 96 - 6, 232 - 23, 96, 18, "POWER WIRING", 8, 8, "N.T.S.")
    return s.render("s8")


if __name__ == "__main__":
    sheets = [sheet1(), sheet2(), sheet3(), sheet4(), sheet5(), sheet6(), sheet7(), sheet8()]
    os.makedirs("drawings", exist_ok=True)
    for i, sv in enumerate(sheets, 1):
        open(f"drawings/sheet{i}.svg", "w").write(standalone(sv))
    open("drawings/_sheets.json", "w").write(json.dumps(sheets))
    print("wrote", len(sheets), "sheets")
